jonnew/cyclops/resources/current_feedback_diagram.pdf

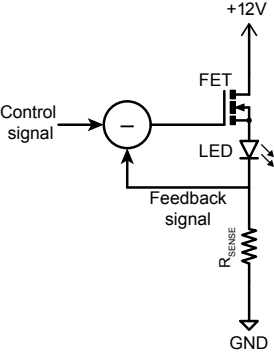
[picture p59: figure]
RSENSE +12V; FET; Control; signal; Feedback signal; GND; LED
