jonnew/cyclops/resources/cyclops_cartoon_concept.pdf

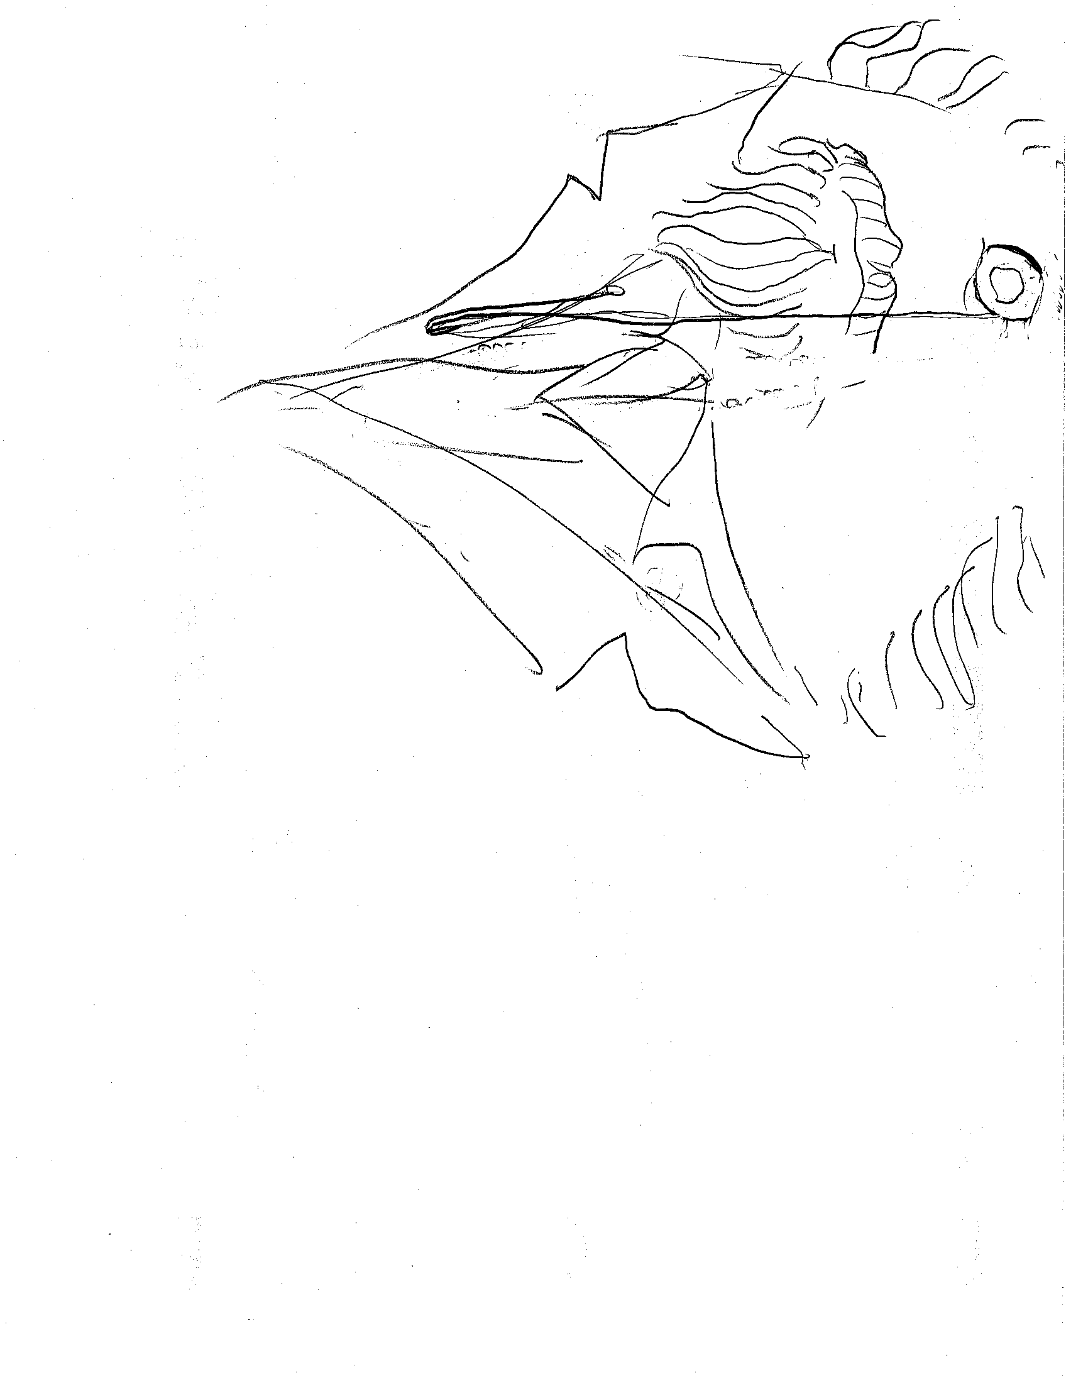
[picture p66: page 1]
