jonnew/cyclops/device/panel/panels.bmp

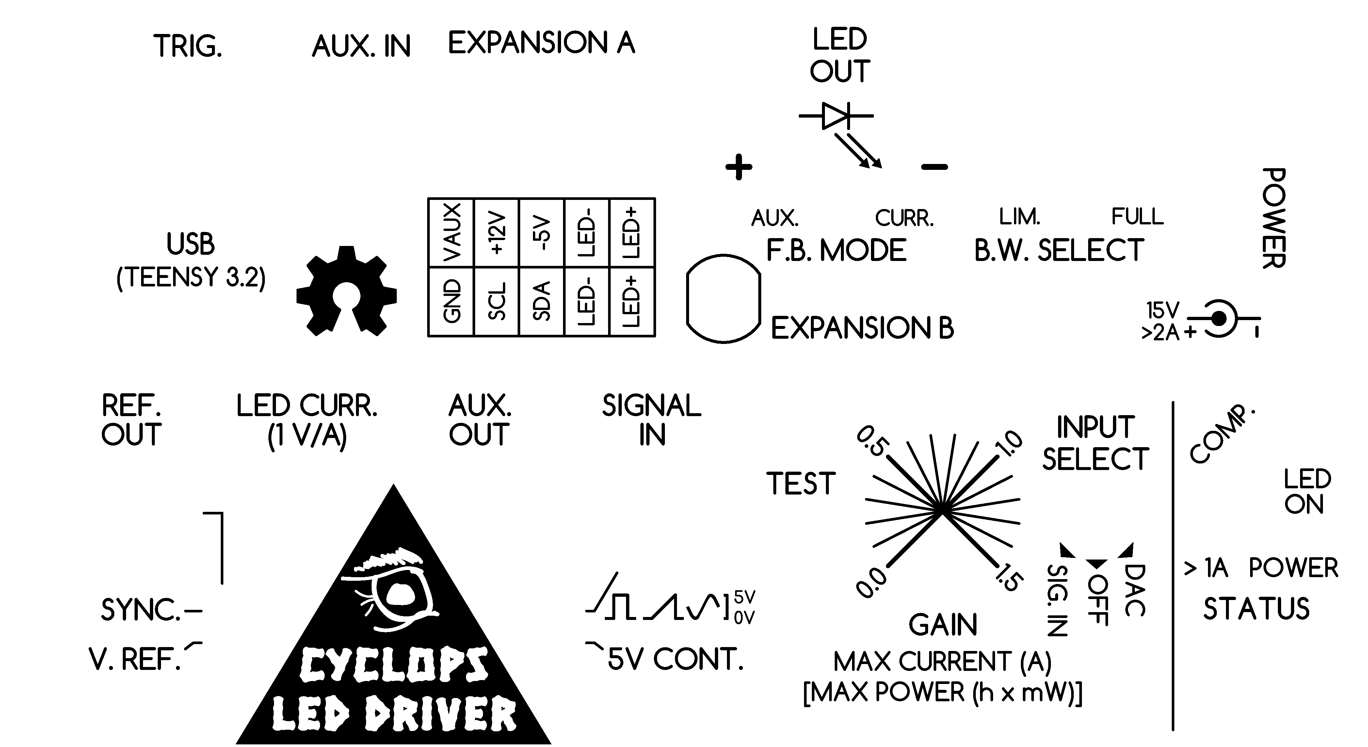
device/panel/panels.bmp
