jonnew/cyclops/device/spice/cyclops_r3.5_drive-circuit_a-ab_ac-analysis.png

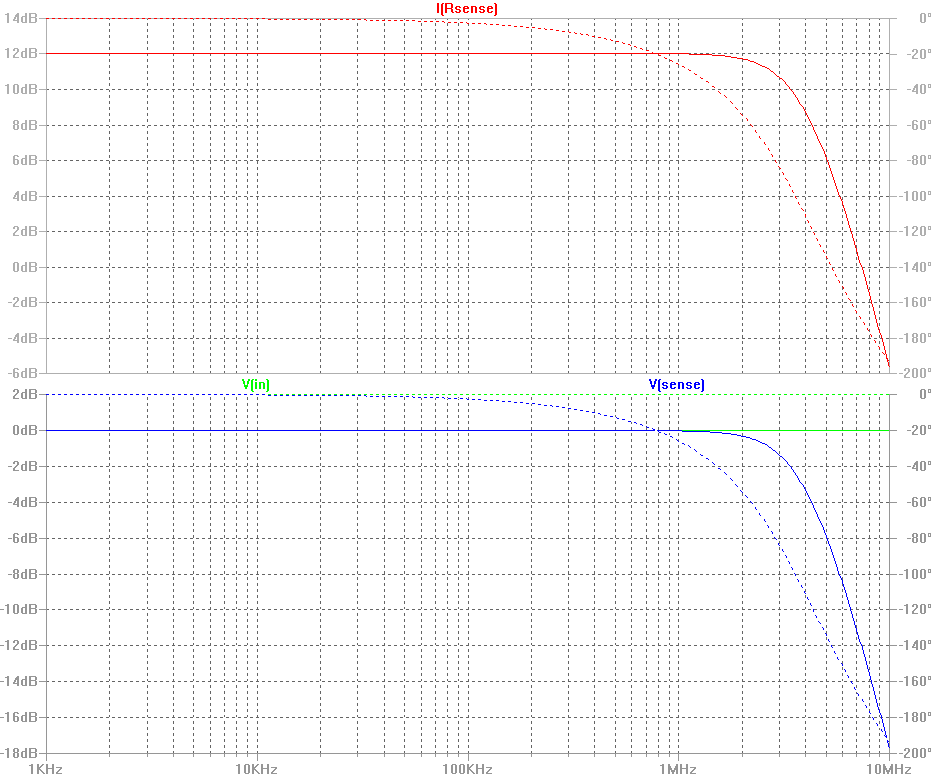
device/spice/cyclops_r3.5_drive-circuit_a-ab_ac-analysis.png
