jonnew/cyclops/device/spice/cyclops_r3.5_negative-rail.png

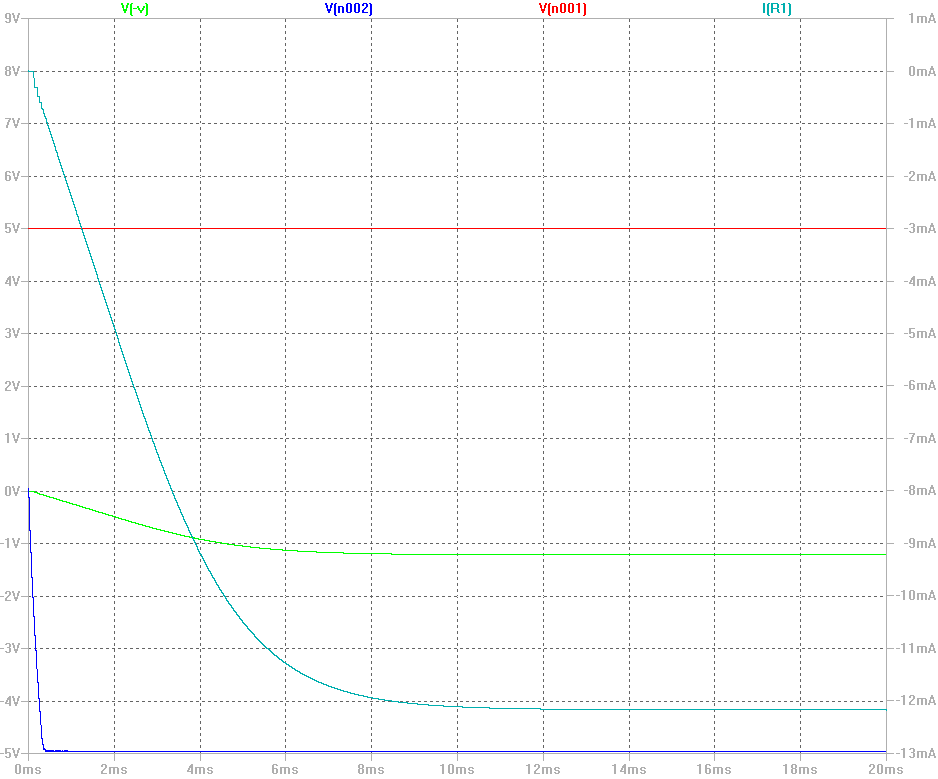
device/spice/cyclops_r3.5_negative-rail.png
