jonnew/cyclops/device/spice/cyclops_r3.5_rsense_0R1_ILED.png

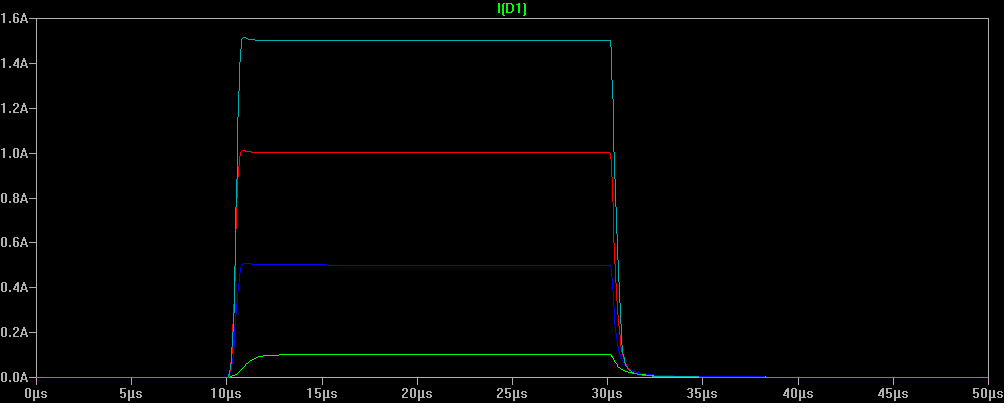
device/spice/cyclops_r3.5_rsense_0R1_ILED.png
