jonnew/cyclops/resources/300px-cyclops_circuit.png

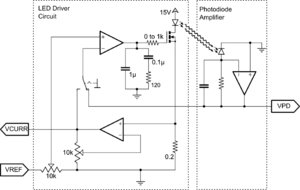
resources/300px-cyclops_circuit.png
