jonnew/cyclops/resources/cyclops3.3_back_raw.JPG

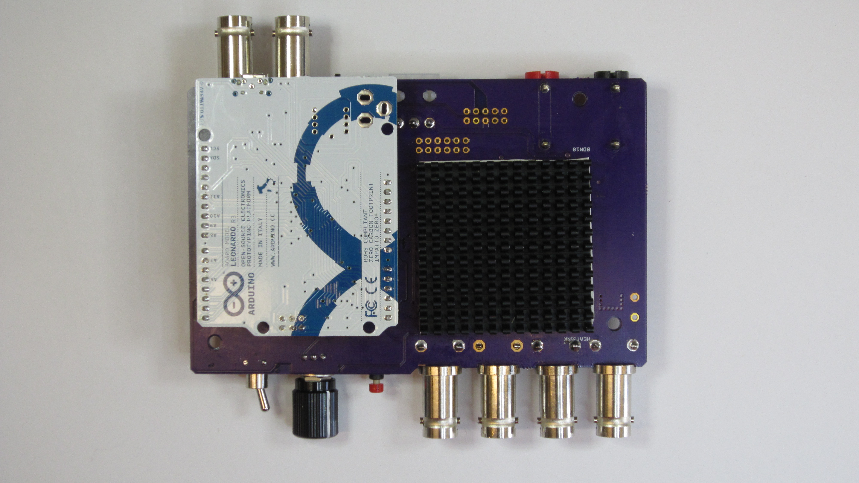
resources/cyclops3.3_back_raw.JPG
