jonnew/cyclops/resources/cyclops3.3_front_raw.JPG

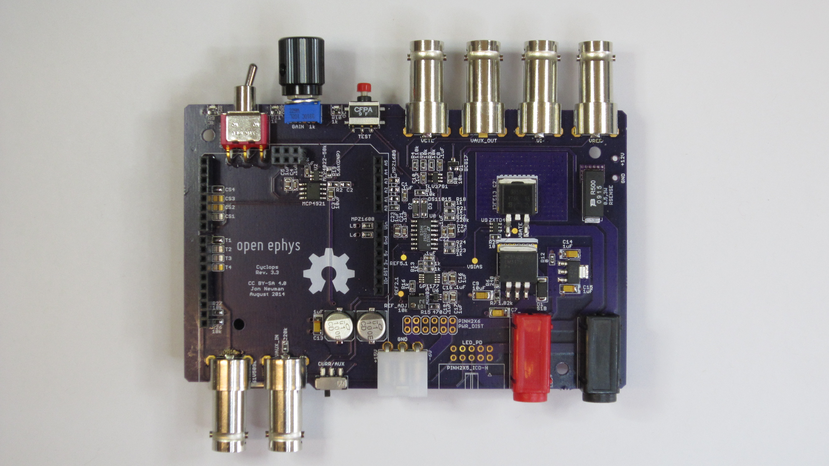
resources/cyclops3.3_front_raw.JPG
