jonnew/cyclops/resources/cyclops3.5A_finished1.jpg

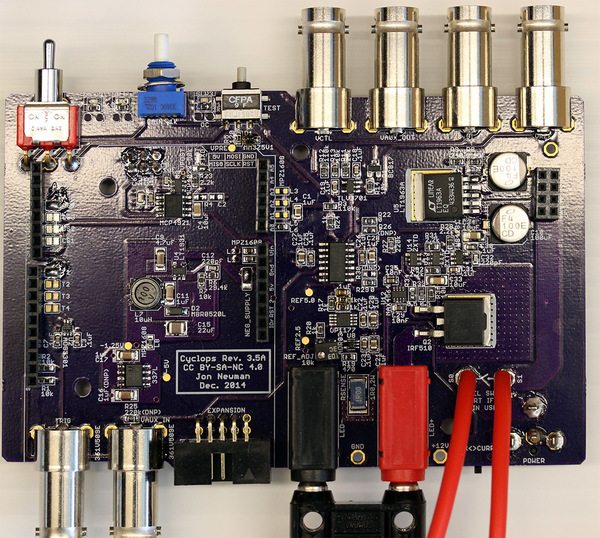
resources/cyclops3.5A_finished1.jpg
