jonnew/cyclops/resources/cyclops3.5A_heatsink.jpg

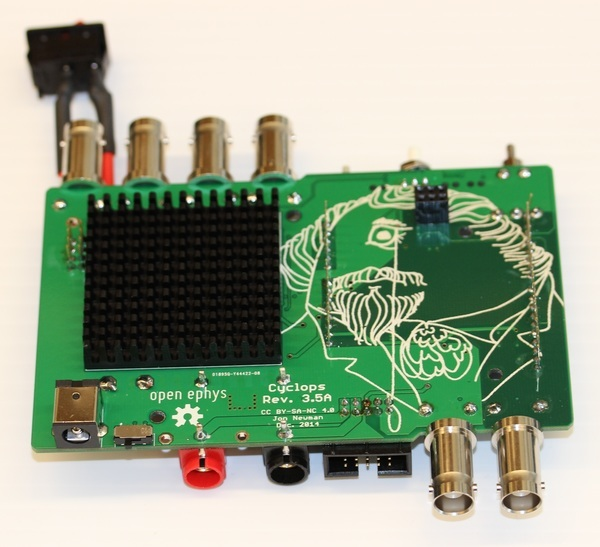
resources/cyclops3.5A_heatsink.jpg
