jonnew/cyclops/resources/cyclops3.5D_all-sink.png

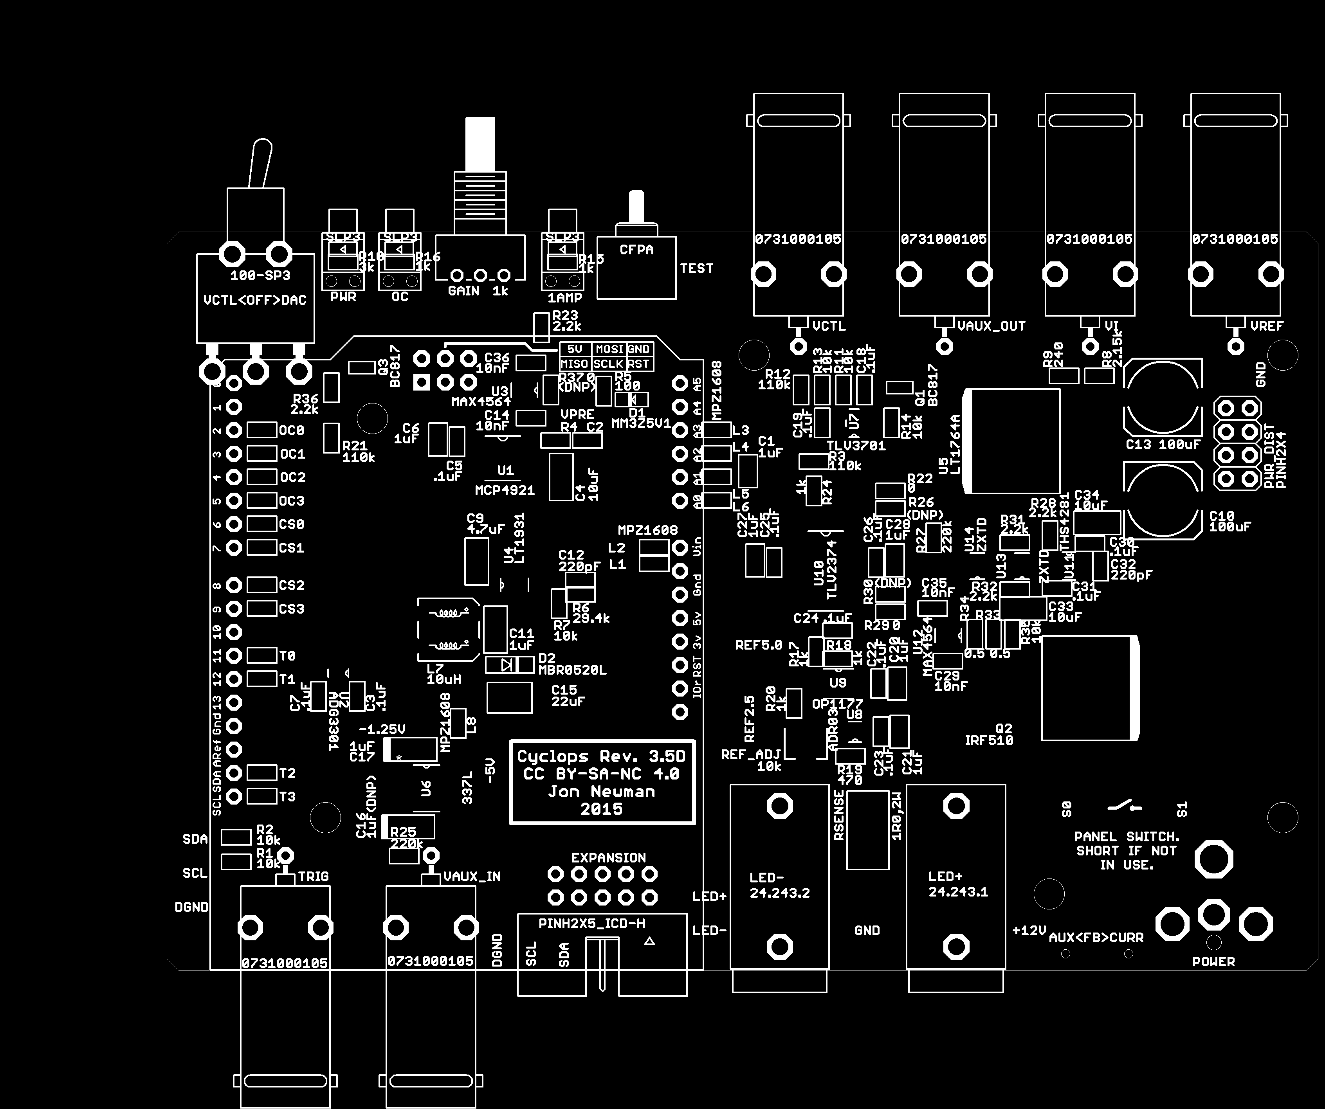
resources/cyclops3.5D_all-sink.png
