jonnew/cyclops/resources/cyclops3.5D_tplace-only.png

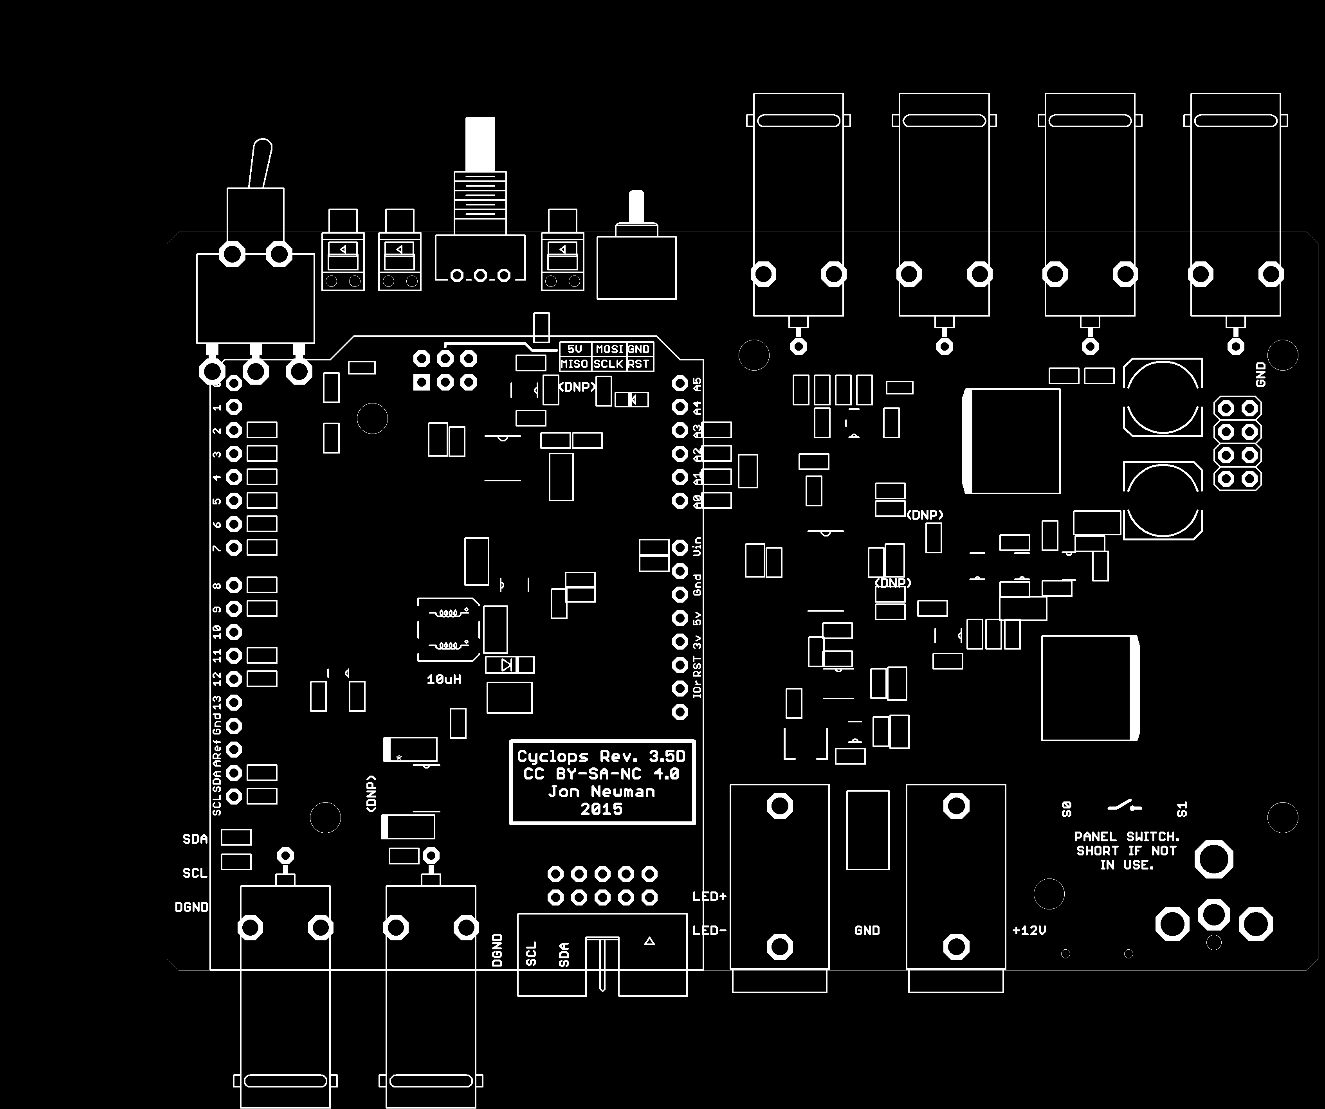
resources/cyclops3.5D_tplace-only.png
