jonnew/cyclops/resources/cyclops_cartoon.bmp

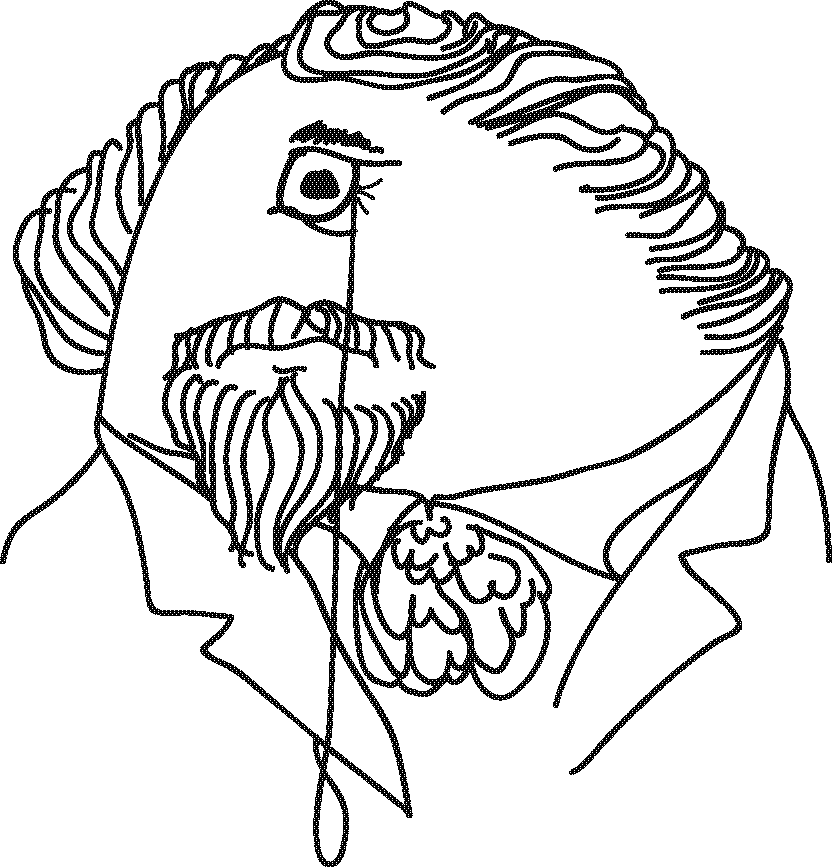
resources/cyclops_cartoon.bmp
