jonnew/cyclops/resources/device3.4_0.jpg

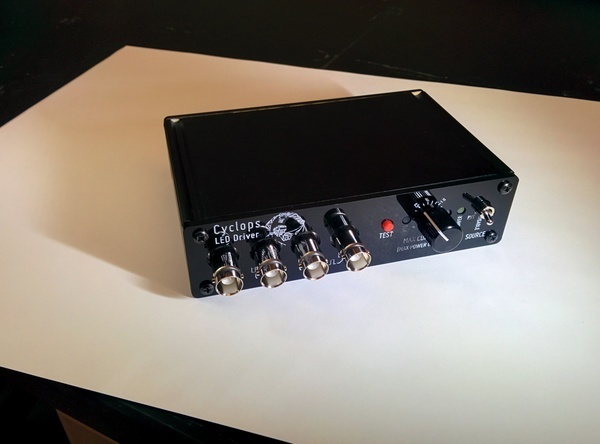
resources/device3.4_0.jpg
