jonnew/cyclops/resources/device3.4_1.jpg

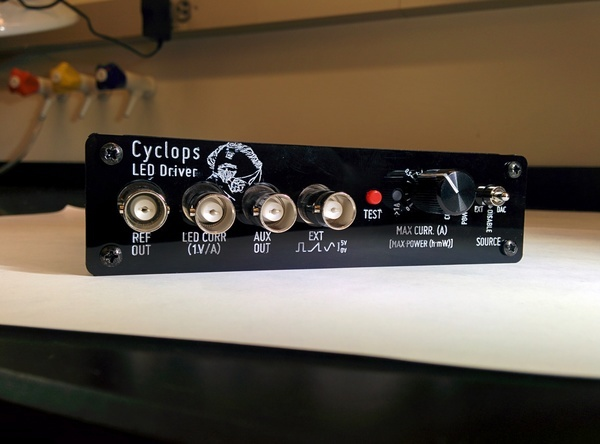
resources/device3.4_1.jpg
