jonnew/cyclops/resources/device3.4_2.jpg

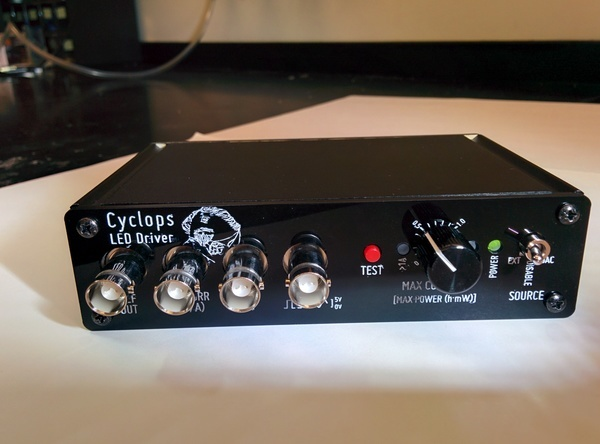
resources/device3.4_2.jpg
