jonnew/cyclops/resources/device3.4_3.jpg

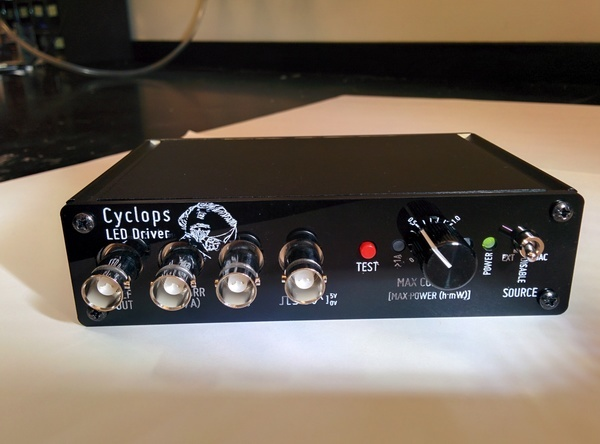
resources/device3.4_3.jpg
