jonnew/cyclops/resources/device3.4_4.jpg

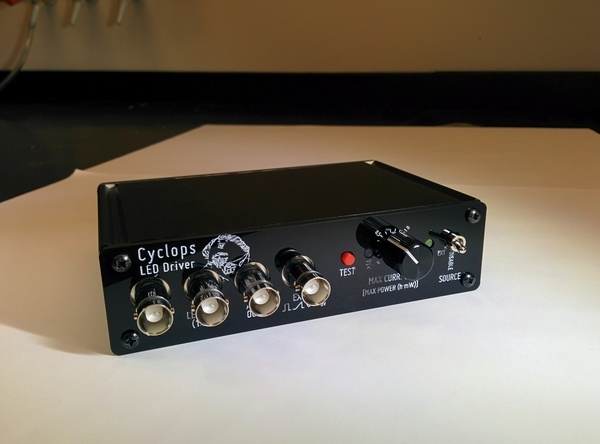
resources/device3.4_4.jpg
