jonnew/cyclops/resources/device3.4_4.png

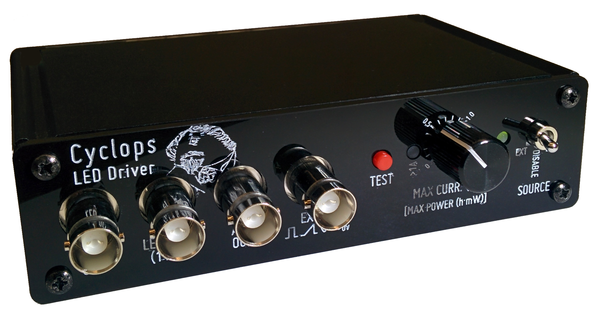
resources/device3.4_4.png
