jonnew/cyclops/resources/device3.5A_back-panel.JPG

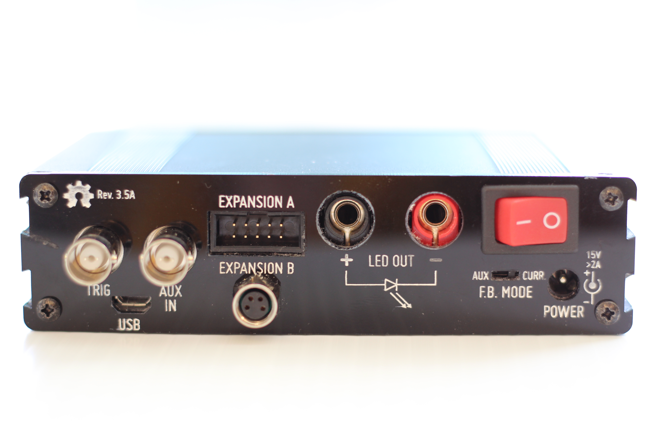
resources/device3.5A_back-panel.JPG
