jonnew/cyclops/resources/device3.5A_front-panel.JPG

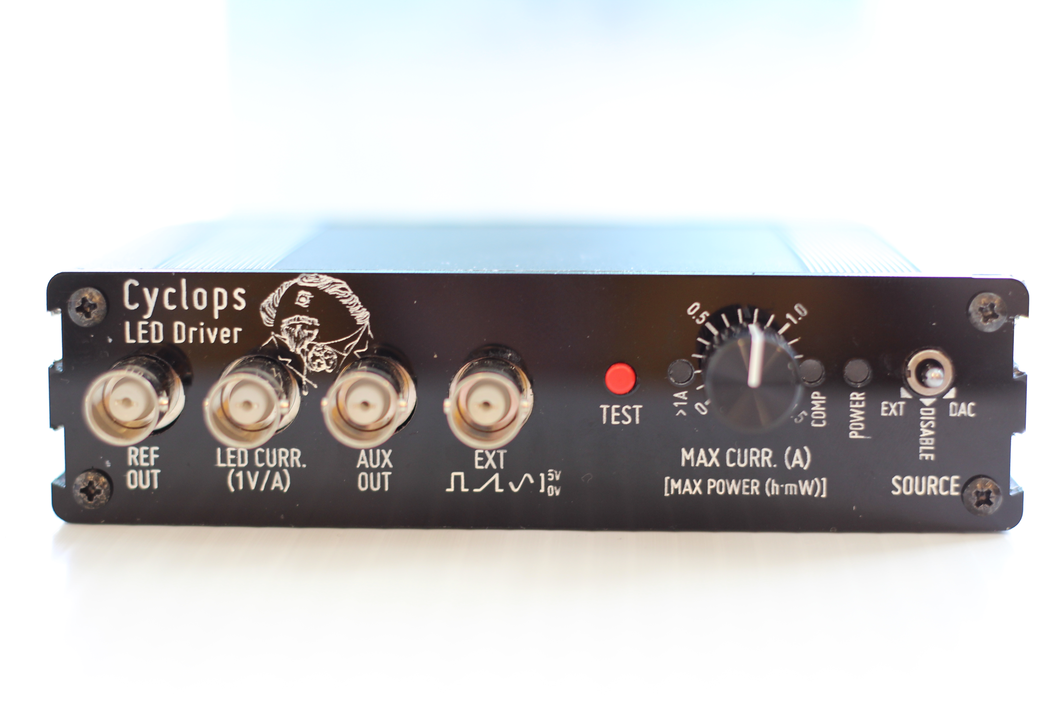
resources/device3.5A_front-panel.JPG
