jonnew/cyclops/resources/fiber-coupled-led-back.png

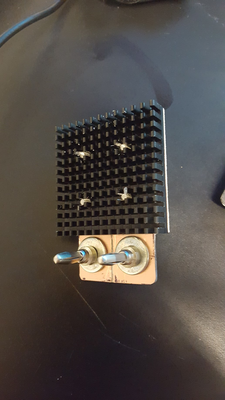
resources/fiber-coupled-led-back.png
