jonnew/cyclops/resources/fiber-coupled-led-front.png

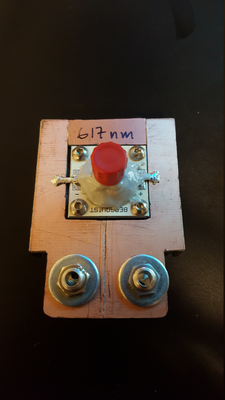
resources/fiber-coupled-led-front.png
