jonnew/cyclops/resources/knob-hardware.jpg

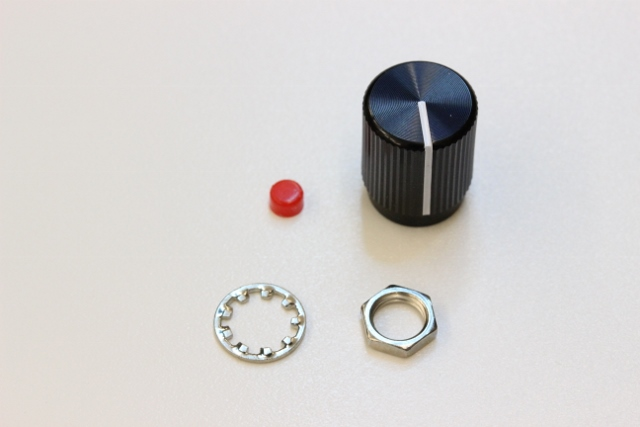
resources/knob-hardware.jpg
