jonnew/cyclops/resources/rage_guy_00.jpg

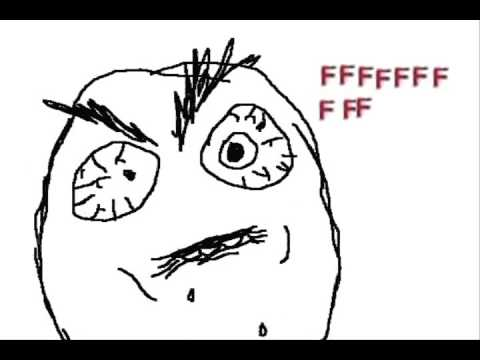
resources/rage_guy_00.jpg
