jonnew/cyclops/resources/teensy-jig-1.jpg

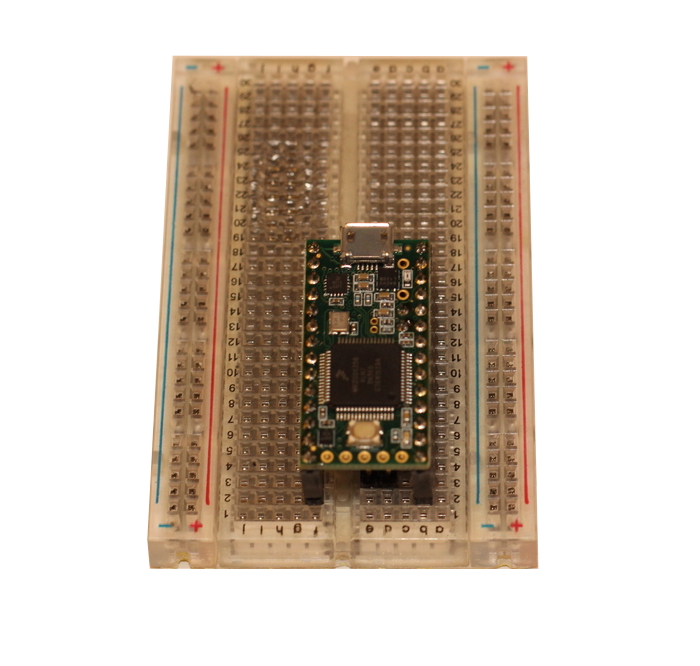
resources/teensy-jig-1.jpg
