jonnew/cyclops/resources/teensy-jig-2.jpg

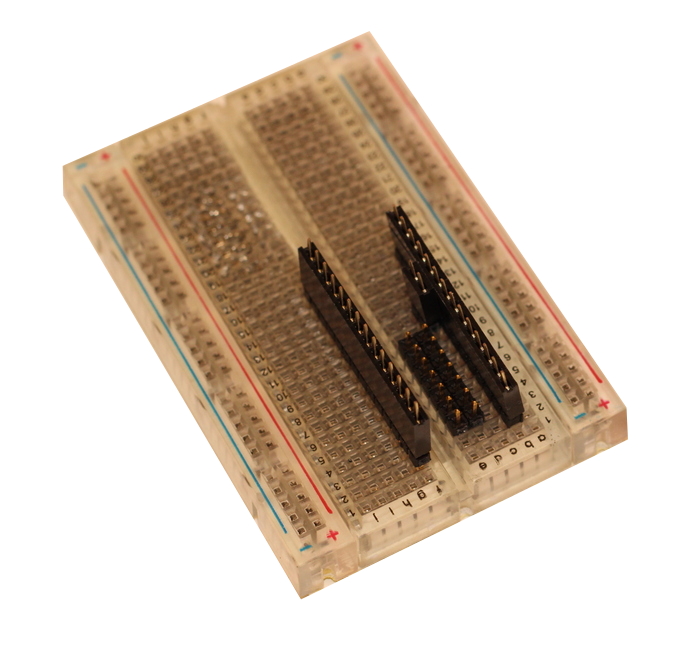
resources/teensy-jig-2.jpg
