jonnew/cyclops/resources/teensy-jig-3.jpg

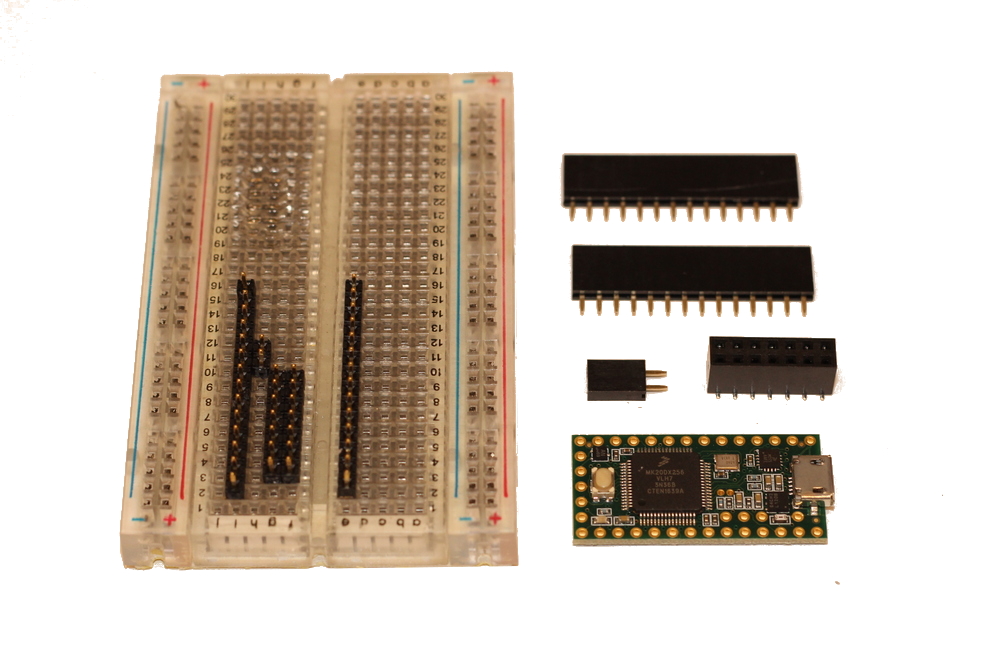
resources/teensy-jig-3.jpg
