jonnew/cyclops/resources/teensy-jig-4.jpg

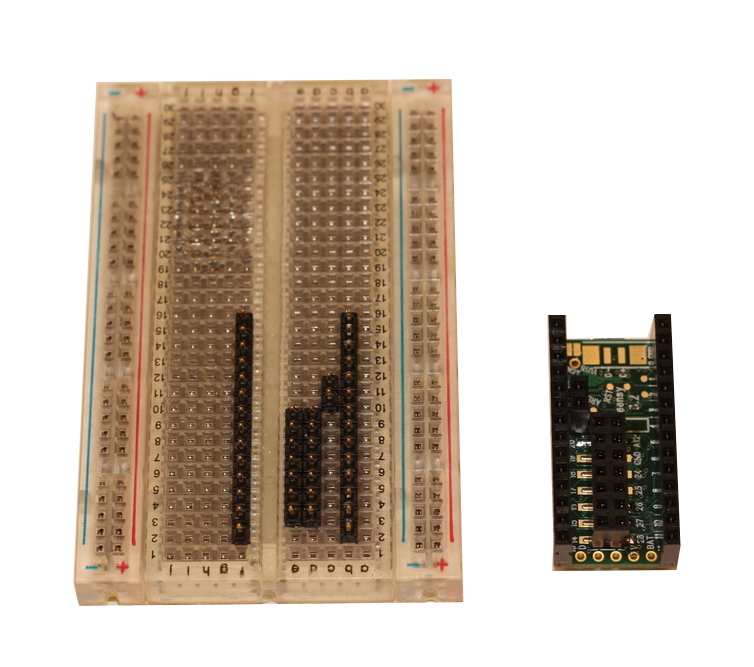
resources/teensy-jig-4.jpg
