jonnew/cyclops/resources/device-components.png

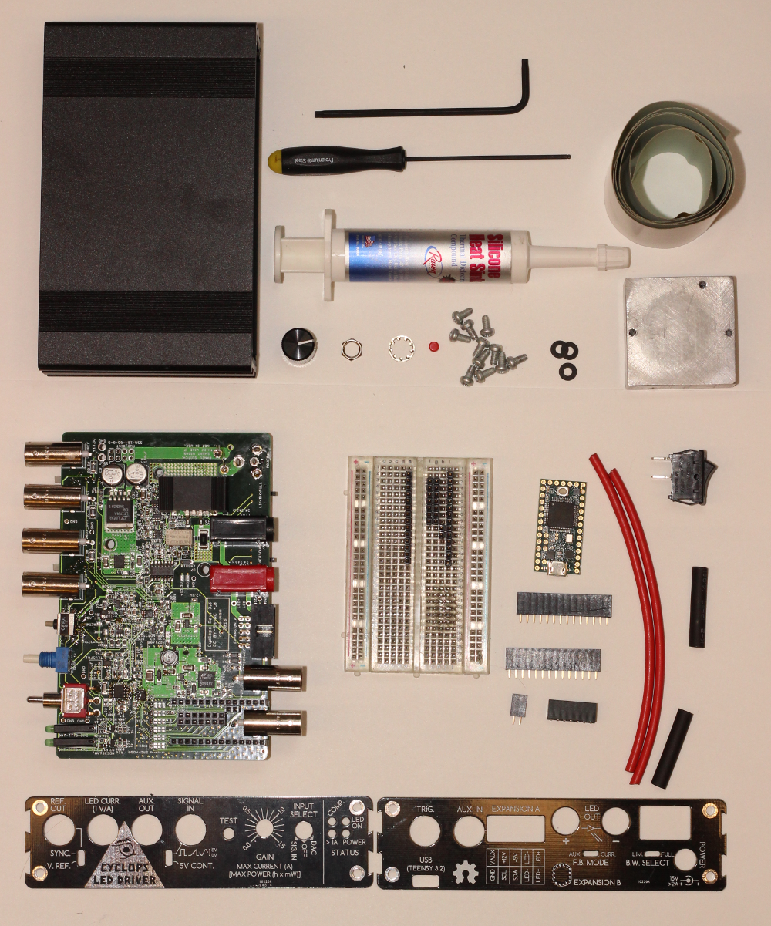
resources/device-components.png
