jonnew/cyclops/resources/switch-parts.jpg

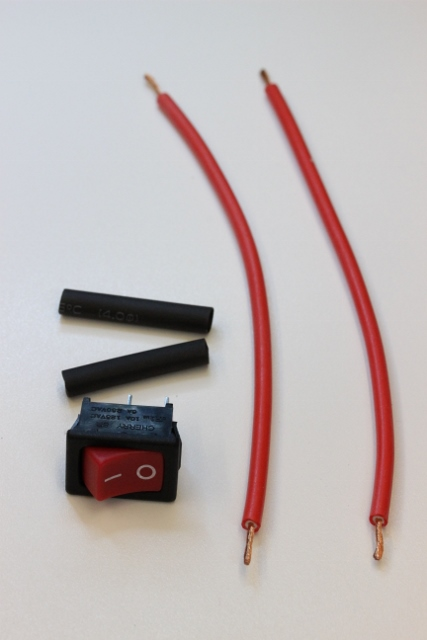
resources/switch-parts.jpg
