jonnew/cyclops/resources/cyclops3.5A_install-arduino.jpg

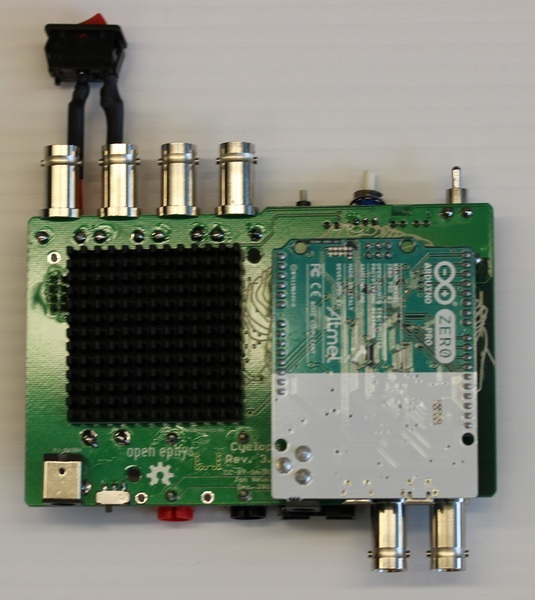
resources/cyclops3.5A_install-arduino.jpg
