jonnew/cyclops/resources/gain-knob-install.jpg

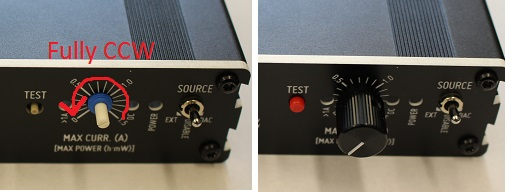
resources/gain-knob-install.jpg
