jonnew/cyclops/resources/knob-install-2.jpg

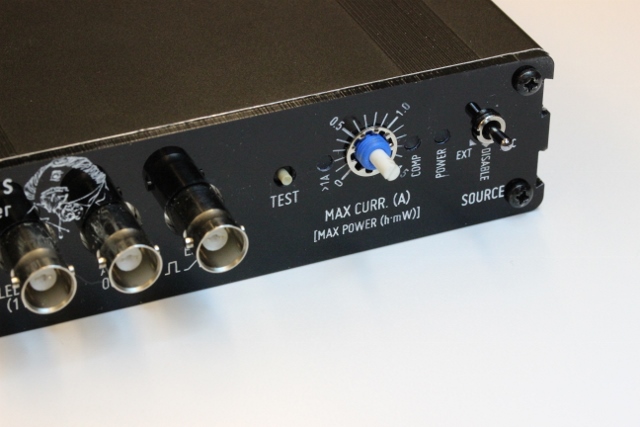
resources/knob-install-2.jpg
