jonnew/cyclops/resources/knob-install-3.jpg

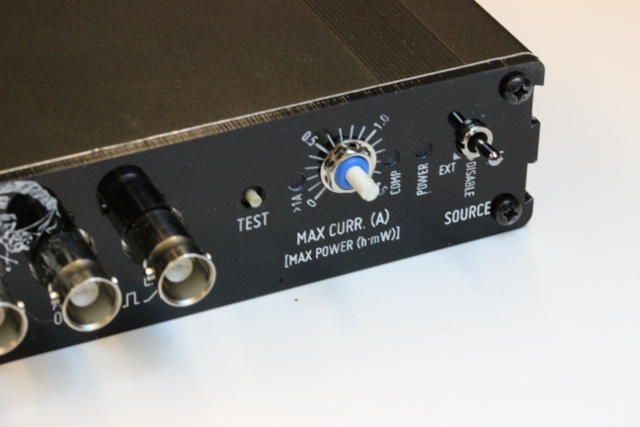
resources/knob-install-3.jpg
