jonnew/cyclops/resources/knob-install-4.jpg

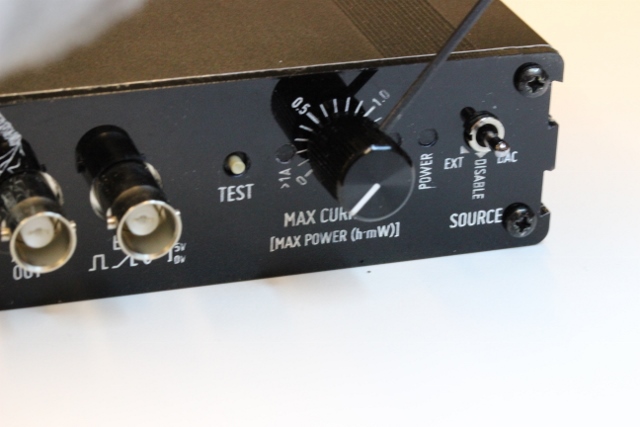
resources/knob-install-4.jpg
