jonnew/cyclops/resources/knob-install-5.jpg

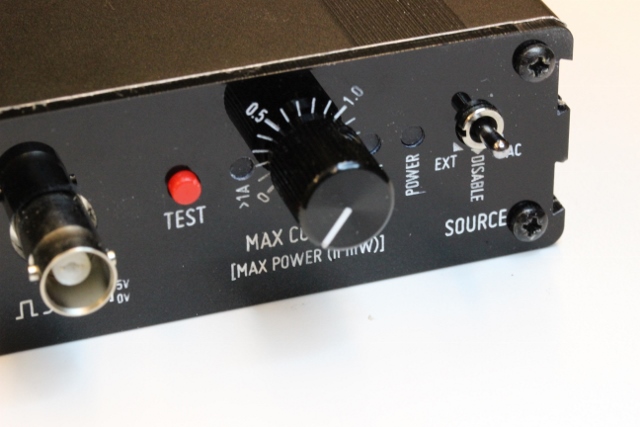
resources/knob-install-5.jpg
