jonnew/cyclops/resources/switch-install-1.jpg

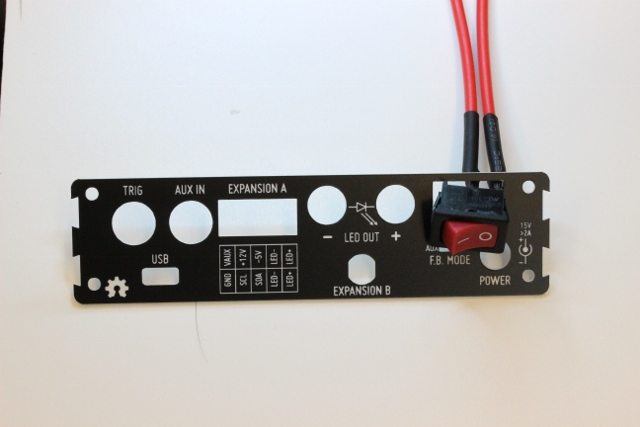
resources/switch-install-1.jpg
