jonnew/cyclops/resources/switch-install-2.jpg

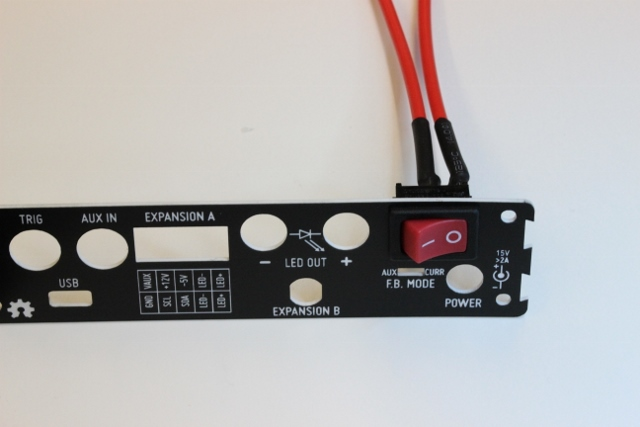
resources/switch-install-2.jpg
