jonnew/cyclops/resources/switch-solder-1.jpg

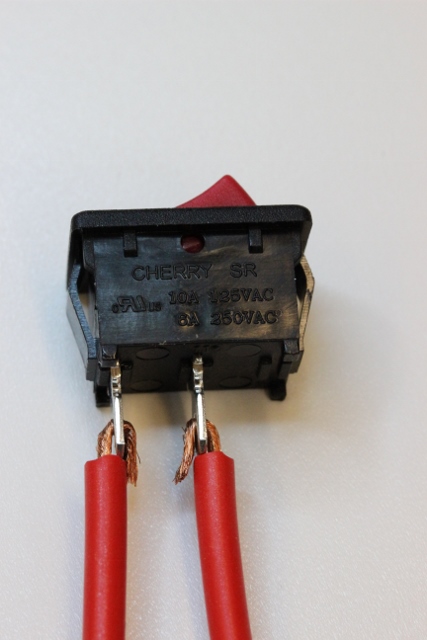
resources/switch-solder-1.jpg
