jonnew/cyclops/resources/switch-solder-2.jpg

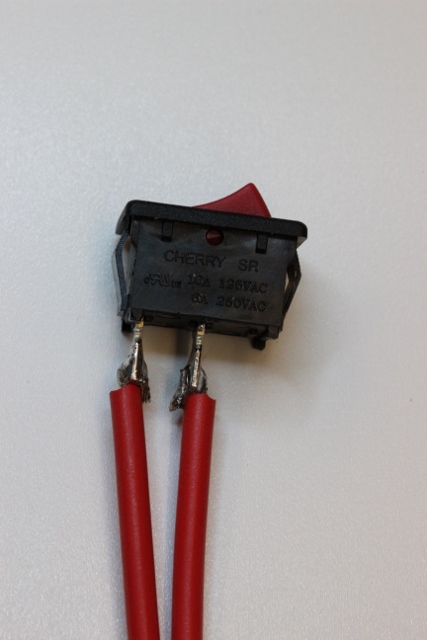
resources/switch-solder-2.jpg
