jonnew/cyclops/resources/switch-solder-3.jpg

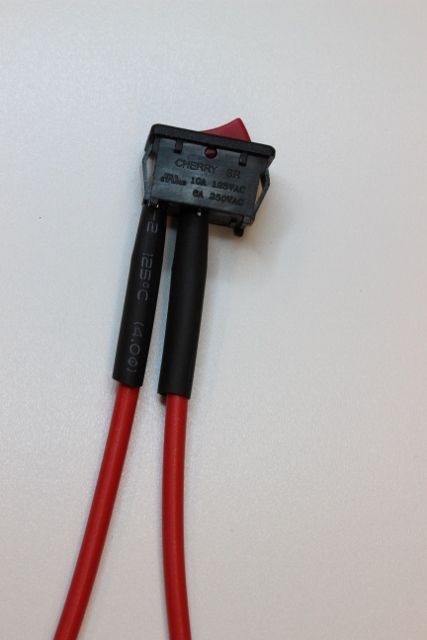
resources/switch-solder-3.jpg
