jonnew/cyclops/resources/switch-solder-4.jpg

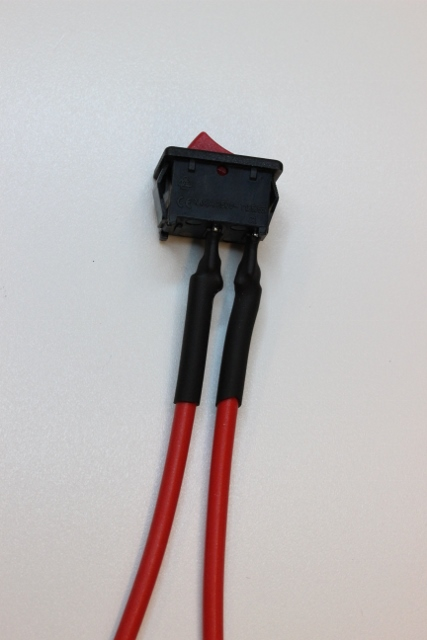
resources/switch-solder-4.jpg
