jonnew/cyclops/resources/optical_feedback_diagram.pdf

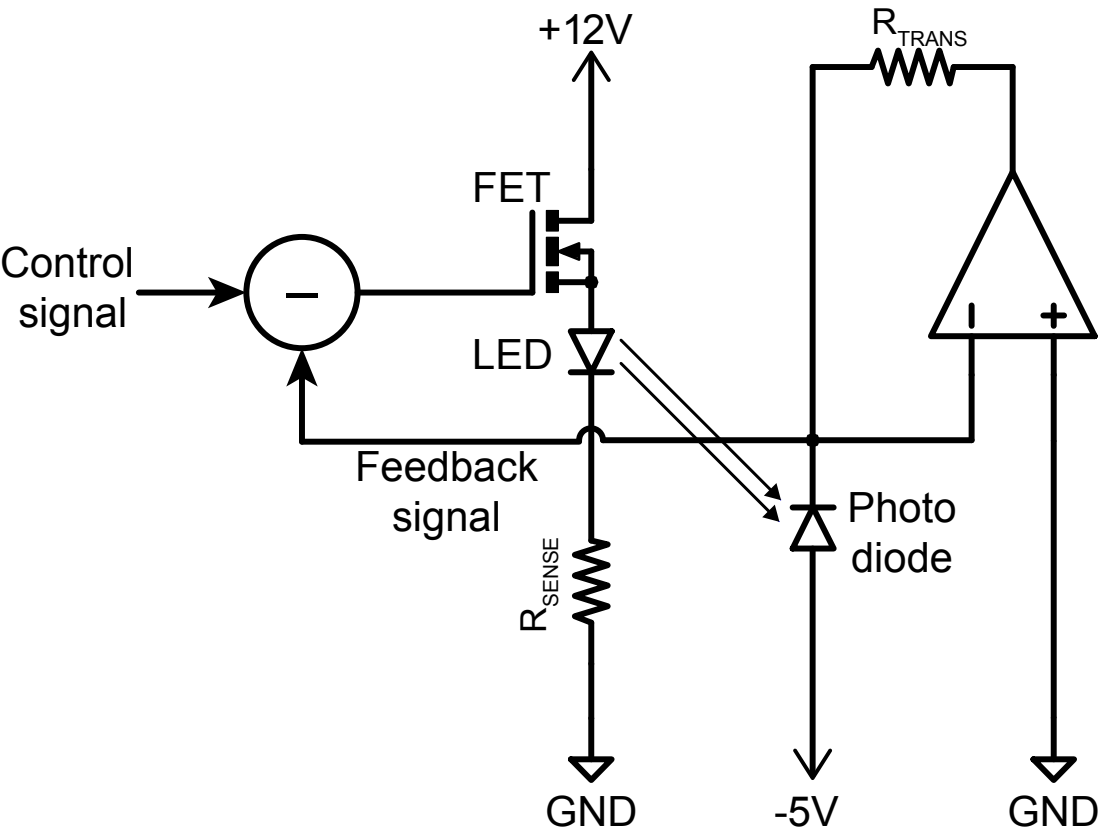
[picture p185: page 1]
RSENSE +12V; FET; Control; signal; Feedback signal; GND; LED; Photo diode; RTRANS
