jonnew/cyclops/device/spice/lt1611_inverter_block_test-fixture.asc

C1: cap; .01µ
C2: cap; 1µ
C3: cap; 10µ
L1: FerriteBead; 1.895µ; Ipk=3 Rser=0.05 Rpar=1616 Cpar=3.6p mfg="Wurth Elektronik" pn="742 792 515"
R1: res; 100
U1: LT1964-BYP
V2: voltage; 5; Rser=0
X3: lt1611_inverter_block
Named nets: 0, -V
LT1964 - 200mA, Low Noise, Low Dropout Negative µPower Regulator
Input: -5V     Output: -1.22V @ 100mA
.tran 2
