jonnew/cyclops/device/spice/an47-65_wideband-current-source-modified.asc

C1: cap; 10p
C2: cap; 2p
C3: cap; 22µ
C4: cap; 22µ
D1: diode; LB_W5SM-typ_TRS
D3: diode; 1N4148
Q1: npn; 2N3866
Q2: npn; 2SC5964
Q3: npn; 2SC5964
Q4: pnp; CM5160
Q5: npn; 2N3866
Q6: pnp; CM5160
R1: res; 100
R2: res; 0.5
R3: res; 0.5
R6: res; 0.1
R7: res; 1.5k
R8: res; 1k
R9: res; 1k
U2: LT1194
U3: LT1190
V1: voltage; PULSE(0 {VIN} 0.5u 1n 1n 1u)
V2: voltage; -2.5v; Rser=0
V3: voltage; 13v; Rser=0
Named nets: 0, -V, +V, FB, IN, OUT
.tran 2u
.inc 2N3866.lib
.inc 2SC5964.lib
.inc LB_W5SM_TRS.lib
.params VIN=0
.step param VIN LIST 0.1 0.5 1.0 1.5
.inc MCH6541.lib
.inc CM5160.lib
