jonnew/cyclops/device/spice/an47-65_wideband-current-source.asc

C1: cap; 100p
C3: cap; 22µ
C4: cap; 22µ
C5: cap; 2p
D1: diode; LB_W5SM-typ_TRS
D2: diode; LB_W5SM-typ_TRS
D3: diode; 1N4148
Q2: npn; 2SC5964
Q3: npn; 2SC5964
R1: res; 25
R2: res; 0.5
R3: res; 0.5
R4: res; 300
R5: res; 300
R6: res; 0.105
R7: res; 1k
R8: res; 1k
R9: res; 1k
RSense1: res; 0.5; pwr=20
U1: LT1193
U2: LT1194
U3: LT1190
V1: voltage; PULSE(0 {VIN} 0.1u 1n 1n 1u)
V2: voltage; -5v; Rser=0
V3: voltage; 13.3V; Rser=0
X1: ZXTD45; MCH6541
X2: ZXTD45; MCH6541
Named nets: 0, -V, +V, FB, IN, OUT, Sense
.tran 2u
.inc 2N3866.lib
.inc 2SC5964.lib
.inc LB_W5SM_TRS.lib
.params VIN=0
.step param VIN LIST 0.1 0.5 1.0 1.5
.inc MCH6541.lib
