jonnew/cyclops/device/spice/cyclops_r3.6_drive-circuit_a-ab.asc

C1: cap; 10µ
C2: cap; 1µ
C3: cap; 100p
C4: cap; 6.8n
C5: cap; 100p
D2: diode; LB_W5SM-typ_TRS
M1: nmos; irf510
R1: res; 50
R2: res; 37.06k
R4: res; {Rg}
R5: res; 2.2k
R6: res; 2.2k
R7: res; 0.5
R8: res; 0.5
R9: res; 4.0k
RSense: res; 1; pwr=20
U1: ZXTD45; ZXTD4591E6
U2: ZXTD45; ZXTD4591E6
U3: LT1963A
V1: voltage; PULSE(0 0.5 0.5u 1n 1n 1u 2u 2)
V2: voltage; 15
V3: voltage; -2.5; Rser=0.01
V4: voltage; SINE(0.75 0.1 1Meg 0 0 0 10)
X2: LMP7707; THS4281
Named nets: 0, +V, BIAS, GATE, SENSE, -V, IN, VGate, Vdummy
.tran 10u
.inc ZXTD4591E6.lib
.inc irf510.lib
.inc THS4281.lib
.inc LB_W5SM_TRS.lib
.params VIN=0
;.step param VIN LIST 0.2 0.2
.model ledCable LTRA(len=1 R=0.01 L=77n C=30.8p)
.step param Rg LIST  0.1 1e6
