jonnew/cyclops/device/spice/cyclops_r3.6_drive-circuit_a-ab_high-side.asc

C1: cap; 10p
C2: cap; 2p
D1: diode; LB_W5SM-typ_TRS
D2: diode; 1N4148
M1: nmos; irf510
R1: res; 50
R2: res; 0
R3: res; 2.2k
R4: res; 10k
R5: res; 2.2k
R6: res; 2.2k
R7: res; 0.5
R8: res; 0.5
R9: res; 1k
R10: res; 1k
R11: res; 50
RSense: res; 0.25; pwr=20
U1: ZXTD45; ZXTD4591E6
U2: ZXTD45; ZXTD4591E6
U5: LT1193
V1: voltage; PULSE(0 {VIN} 0.5u 1n 1n 1u)
V2: voltage; 13.5; Rser=0.01
V3: voltage; -2.5; Rser=0.01
X1: LMP7707; THS4281
Named nets: 0, +V, GATE, -V, IN, FB, Sense
.tran 2.1u
.inc ZXTD4591E6.lib
.inc irf510.lib
.inc THS4281.lib
.inc LB_W5SM_TRS.lib
.params VIN=0
.step param VIN LIST 0.1 0.5 1.0 1.5
