jonnew/cyclops/device/spice/cyclops_r3.6_drive-circuit_booster-stage.asc

C1: cap; 10µ
C2: cap; 1µ
C3: cap; 100p
R1: res; 50
R2: res; 37.06k
R5: res; 1k
R6: res; 1k
R7: res; 0.5
R8: res; 0.5
R9: res; 4.0k
U1: ZXTD45; ZXTD4591E6
U2: ZXTD45; ZXTD4591E6
U3: LT1963A
V1: voltage; PULSE(0 {VIN} 10n 5n 5n 50n)
V2: voltage; 15
V3: voltage; -2.5; Rser=0.1
Named nets: 0, +V, -V, IN, VGate
.tran 80n
.inc ZXTD4591E6.lib
.inc irf510.lib
.inc THS4281.lib
.inc LB_W5SM_TRS.lib
.params VIN=0
.step param VIN LIST 1 2 3 4 5 6 7 8 9 10
;MEASURE TRAN tdlay TRIG i(Rsense)  VAL = 0.01 RISE = 1 TD=0.25u
.model ledCable LTRA(len=1 R=0.01 L=77n C=30.8p)
