jonnew/cyclops/device/spice/cyclops_r3.6_feedback-factor.asc

D2: diode; LB_W5SM-typ_TRS
M1: nmos; irf510
R1: res; 10
RSense: res; 1.0; pwr=20
V1: voltage; PULSE(0 {AMPL} 1n 1n
V3: voltage; 12
X1: ZXTD45; ZXTD4591E6
Named nets: 0, +V, GATE
.inc M:\\public\\cyclops\\cyclops_r3\\spice\\sihf540s.lib
;op
.inc M:\\public\\cyclops\\cyclops_r3\\spice\\LB_W5SM_TRS.lib
.inc M:\\public\\cyclops\\cyclops_r3\\spice\\TLV2370.lib
.inc M:\\public\\cyclops\\cyclops_r3\\spice\\ZXTD4591E6.lib
.inc M:\\public\\cyclops\\cyclops_r3\\spice\\irf510.lib
.inc C:\\Users\\jon\\Downloads\\si2336ds_ps_revb\\si2336ds_ps_rc Rev B.lib
.inc M:\\public\\cyclops\\cyclops_r3\\spice\\sum50n06.lib
.inc M:\\public\\cyclops\\cyclops_r3\\spice\\LMP7709.lib
.PARAMS AMPL=0
.tran 2u
.step param AMPL LIST 6 6.5 7 7.5 8 8.5 9 9.5 10 10.5 11 11.5 12 12.5
