jonnew/cyclops/device/spice/led-active.asc

C1: cap; 10n
D2: LED
M2: nmos; SSM3K324R
R1: res; 1k
R2: res; 100k
R3: res; 100
R4: res; 100k
R5: res; 1k
R6: res; 100k
R7: res; 100
U1: LT1711
V1: voltage; PULSE(0 0.02 1u 0.1n 0.1n 1000n)
V2: voltage; 5V; Rser=0.0
V3: voltage; -2.5; Rser=0
V4: voltage; 12V; Rser=0
Named nets: 0, -V, IN, +V, +12V, +12v, LED_EN
.tran 2u
.inc ZXTD4591E6.lib
.inc irf510.lib
.inc THS4281.lib
.inc LB_W5SM_TRS.lib
.inc SSM3K324R.lib
