jonnew/cyclops/device/spice/cyclops_r3.5_input-circuit.asc

R1: res; 100
R2: res; 2.2k
R3: res; 1k
R4: res; 1k
R5: res; 220k
R6: res; 45
V1: voltage; {VIN}
V2: voltage; -1.25V
Z1: zener; mm3z5v1t1
Named nets: 0, VZen, VOUT
.op
.params VIN=0
.step param VIN LIST -5 -4 -3 -2 -1 0 1 2 3 4 5 6 7 8 9 10
.inc MM3Z5V1LT1.lib
