jonnew/cyclops/device/spice/cyclops_r3.5_drive-circuit.asc

D1: diode; LB_W5SM-typ_TRS
M1: nmos; irf510
R1: res; 10
RSense: res; 0.1; pwr=20
U2: ZXTD45; ZXTD4591E6
V1: voltage; PULSE(0 {VIN} 0.25u 1n 1n 2u)
V2: voltage; 11
V3: voltage; -1
V4: voltage; SINE(0.05 0.025 1Meg 0 0 0)
X2: LMP7707
Named nets: 0, +V, BIAS, GATE, SENSE, EMITTER, -V, IN
;op
.tran 0 3u 0
.inc ZXTD4591E6.lib
.inc irf510.lib
.inc LMP7707.lib
.inc LB_W5SM_TRS.lib
.params VIN=0
.step param VIN LIST 0.01 0.1 0.15
