jonnew/cyclops/device/spice/cyclops_r3.5_drive-circuit_a-ab.asc

C1: cap; 10µ
C2: cap; 1µ
C3: cap; 220pf
D1: diode; LB_W5SM-typ_TRS
M1: nmos; irf510
R2: res; 37.06k
R3: res; 2.2k
R4: res; 10k
R5: res; 2.2k
R6: res; 2.2k
R7: res; 0.5
R8: res; 0.5
R9: res; 4.0k
RSense: res; 1; pwr=20
U1: ZXTD45; ZXTD4591E6
U2: ZXTD45; ZXTD4591E6
U3: LT1963A
V1: voltage; PULSE(0 {VIN} 1u 1n 1n 5u 10u 2)
V2: voltage; 15
V3: voltage; -1.25; Rser=0.1
V4: voltage; SINE(0.125 0.025 1Meg 0 0 0); AC 1
V5: voltage; 0.4
X2: LMP7707; THS4281
Named nets: 0, +V, BIAS, GATE, SENSE, -V, IN
.tran 20u
.inc ZXTD4591E6.lib
.inc irf510.lib
.inc THS4281.lib
.inc LB_W5SM_TRS.lib
.params VIN=0
.step param VIN LIST 0.1 0.5 1 1.5
;MEASURE TRAN tdlay TRIG i(Rsense)  VAL = 0.01 RISE = 1 TD=0.25u
.model ledCable LTRA(len=1 R=0.01 L=77n C=30.8p)
