jonnew/cyclops/device/spice/cyclops_r3.5_drive-circuit_a-ab_high-side_01.asc

C1: cap; 10µ
C2: cap; 1µ
C3: cap; 100p
C4: cap; 100p
C5: cap; 0.1µ
C6: cap; 0.1µ
C7: cap; 0.1µ
C8: cap; 0.1µ
D1: diode; LB_W5SM-typ_TRS
L1: ind; 51n
M1: nmos; irf510
R1: res; 500
R2: res; 37.06k
R3: res; 2.2k
R5: res; 2.2k
R6: res; 2.2k
R7: res; 0.5
R8: res; 0.5
R9: res; 4.0k
R10: res; 1k
R11: res; 1k
R12: res; 680
RSense: res; 1; pwr=2
U1: ZXTD45; ZXTD4591E6
U2: ZXTD45; ZXTD4591E6
U3: LT1963A
V1: voltage; PULSE(0 {VIN} 1u 1n 1n 5u)
V2: voltage; 15
V3: voltage; -5V; Rser=0.1
X1: differential-amp; AD830J
X2: LMP7707; THS4281
Named nets: 0, +V, BIAS, GATE, SENSE, -V, IN
.tran 8u
.inc ZXTD4591E6.lib
.inc irf510.lib
.inc THS4281.lib
.inc LB_W5SM_TRS.lib
.params VIN=0
.step param VIN LIST 0.1 0.5 1 3
.inc ad830j.lib
