jonnew/cyclops/device/spice/lt1611_inverter_block.asc

22u: cap; 22µ
C1: cap; 22µ
C2: cap; 1µ
C3: cap; 1200p
D1: schottky
L1: ind2; 22µ
L2: ind2; 22µ
R1: res; 10k
R2: res; 29.4k
U1: LT1611
Named nets: 0, VOUT, VIN
.tran 0 50m 40m
