jonnew/cyclops/device/spice/cyclops_r3.5_lt1611_inverter.asc

22u: cap; 22µ
C1: cap; 22µ
C2: cap; 1µ
C3: cap; 1200p
D1: schottky
L1: ind2; 22µ
L2: ind2; 22µ
R1: res; 10k
R2: res; 10k
U1: LT1611
V1: voltage; 3.3; Rser=0.2
Named nets: 0, OUT, IN
.tran 0 1m 0.5m
