jonnew/cyclops/device/spice/cyclops_r3.5_rsense_0R1.asc

D1: diode; LB_W5SM-typ_TRS
M1: nmos; irf510
R1: res; 1
R4: res; 1k
R5: res; 1k
R6: res; 1k
R7: res; 1k
RSense: res; 0.1; pwr=20
U1: LTC2052
U2: LMP7707
U3: LTC2052
V1: voltage; PULSE(0 {AMPL} 10u 0.0000001 0.0000001 20u)
V2: voltage; SINE(1 0.1 100k 0)
V3: voltage; 12
X1: ZXTD45; ZXTD4591E6
Named nets: 0, RSense, +V, GATE, CMD, REF, -V, CURR
.inc M:\\public\\cyclops\\cyclops_r3\\spice\\sihf540s.lib
;op
.inc M:\\public\\cyclops\\cyclops_r3\\spice\\LB_W5SM_TRS.lib
.tran 0 0.00005 0
.inc M:\\public\\cyclops\\cyclops_r3\\spice\\TLV2370.lib
.inc M:\\public\\cyclops\\cyclops_r3\\spice\\ZXTD4591E6.lib
.inc M:\\public\\cyclops\\cyclops_r3\\spice\\irf510.lib
.inc C:\\Users\\jon\\Downloads\\si2336ds_ps_revb\\si2336ds_ps_rc Rev B.lib
.inc M:\\public\\cyclops\\cyclops_r3\\spice\\sum50n06.lib
.inc M:\\public\\cyclops\\cyclops_r3\\spice\\LMP7709.lib
.PARAMS AMPL=0
.step param AMPL LIST 0.01 0.05 0.1 0.15
